abierto-cc/joselito/embebido/hardware/pdf/amplifier_schematics.png

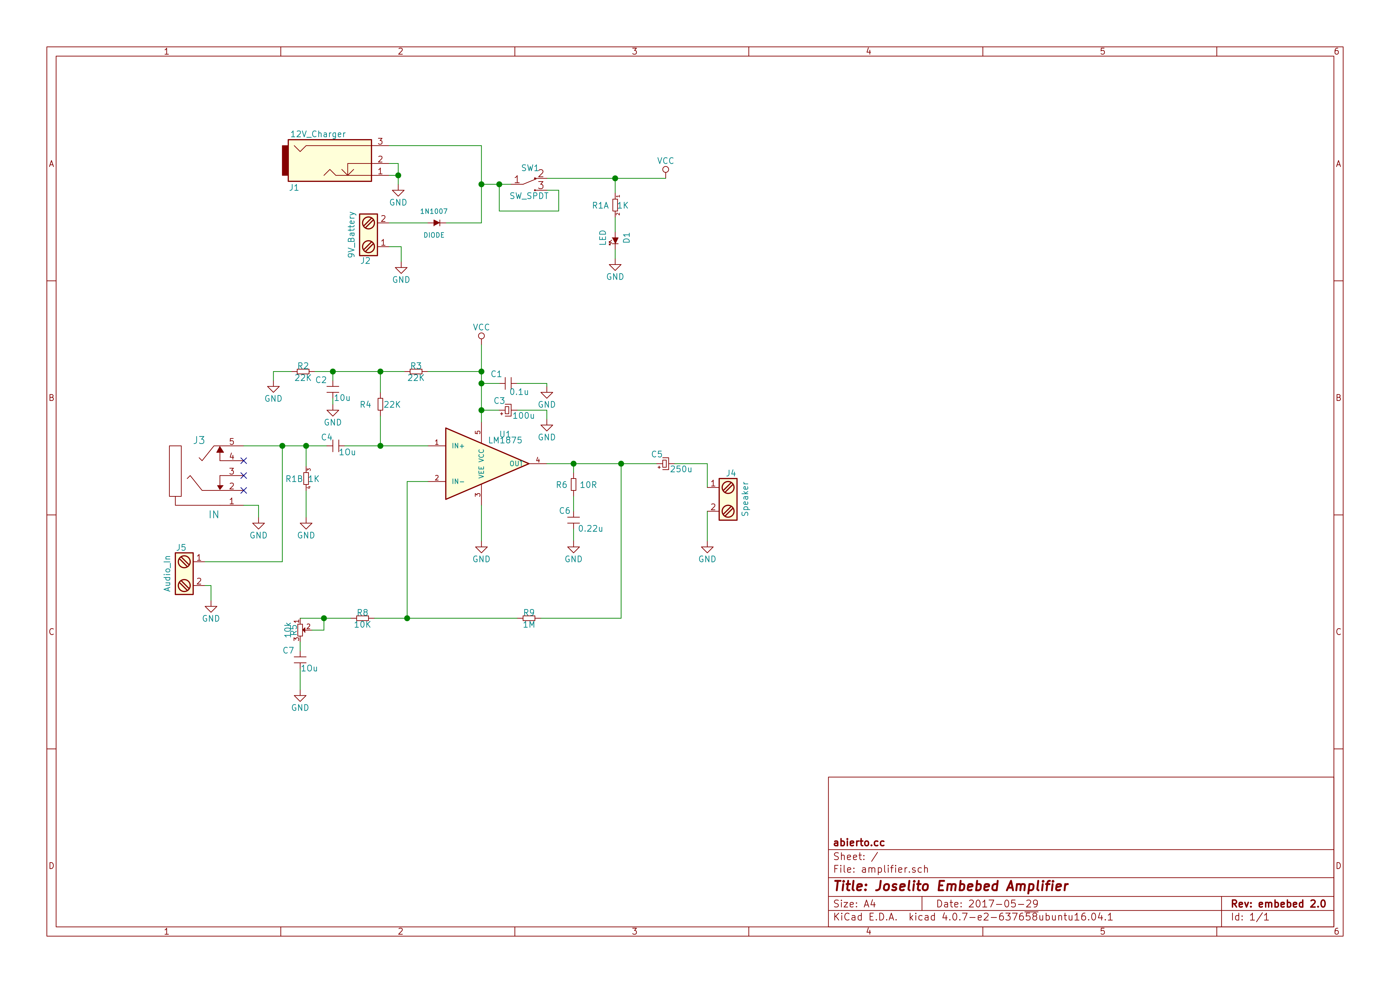
embebido/hardware/pdf/amplifier_schematics.png
